curiouselectric/batlistener/Bat Listener Instructions/Photos/parts1.png

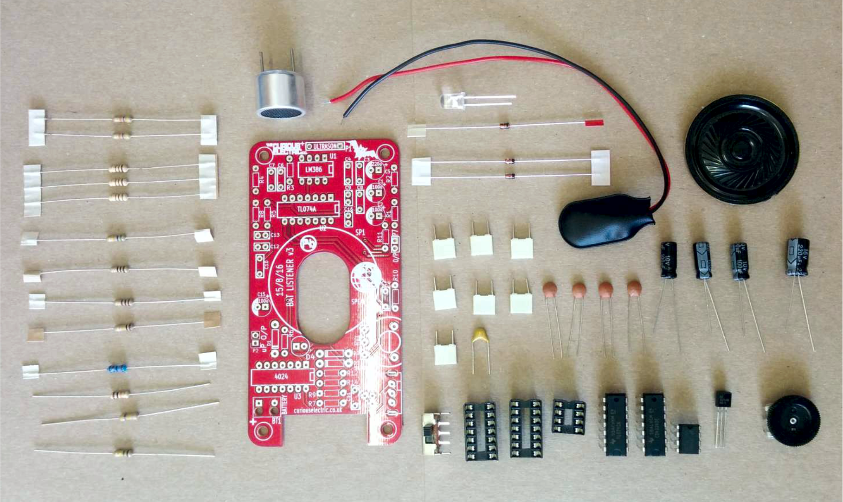
Bat Listener Instructions/Photos/parts1.png
