curiouselectric/batlistener/Bat Listener Instructions/Photos/parts2.png

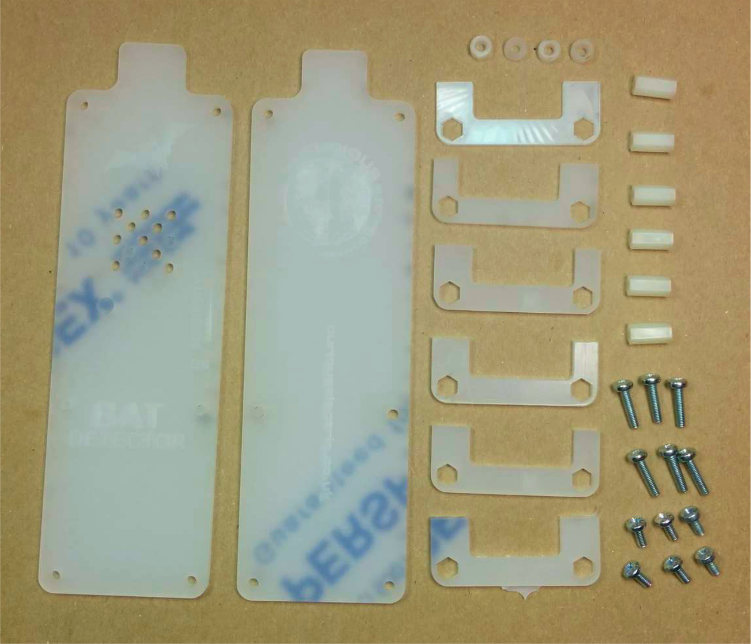
Bat Listener Instructions/Photos/parts2.png
