curiouselectric/batlistener/Bat Listener Instructions/Photos/parts2_1000x500.jpg

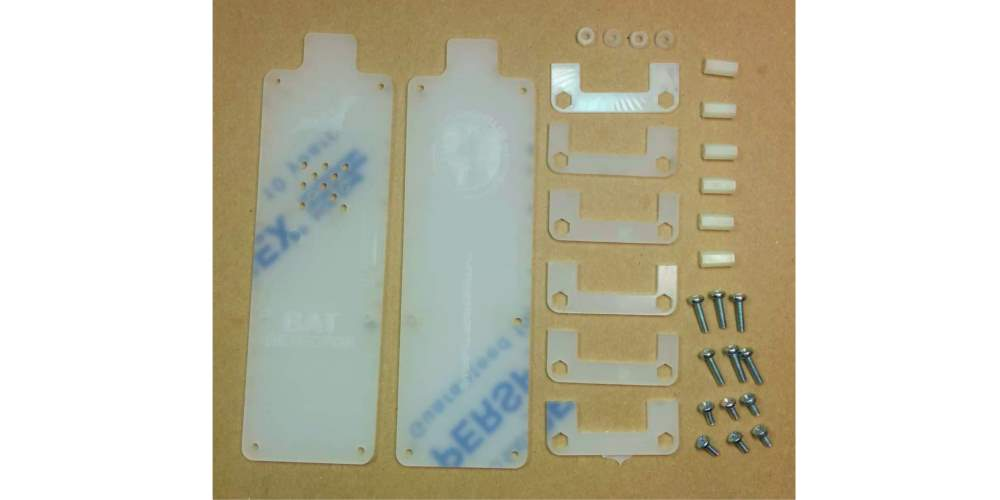
Bat Listener Instructions/Photos/parts2_1000x500.jpg
