curiouselectric/batlistener/Bat Listener Instructions/Capacitor Info/ceramic blob.png

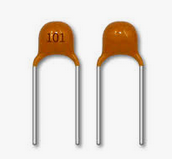
Bat Listener Instructions/Capacitor Info/ceramic blob.png
