curiouselectric/batlistener/Bat Listener Instructions/Capacitor Info/ceramic cap.png

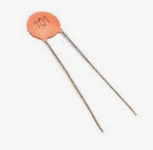
Bat Listener Instructions/Capacitor Info/ceramic cap.png
