curiouselectric/batlistener/Bat Listener Instructions/Capacitor Info/electrolytic cap.png

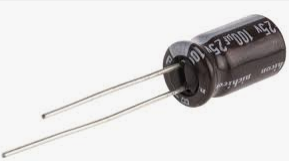
Bat Listener Instructions/Capacitor Info/electrolytic cap.png
