curiouselectric/batlistener/Bat Listener Instructions/Capacitor Info/poly cap.png

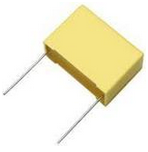
Bat Listener Instructions/Capacitor Info/poly cap.png
