curiouselectric/batlistener/Bat Listener Instructions/Photos/Tools.JPG

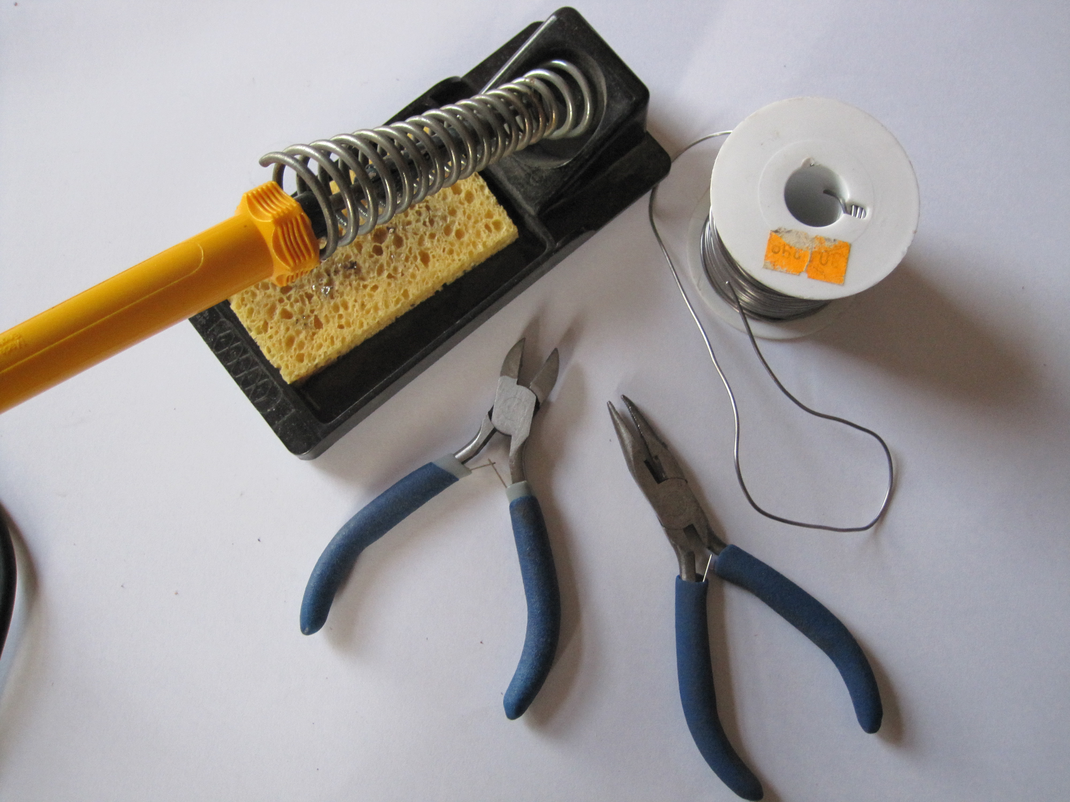
Bat Listener Instructions/Photos/Tools.JPG
